Bastardkb/Dilemma/pics/1e.jpg

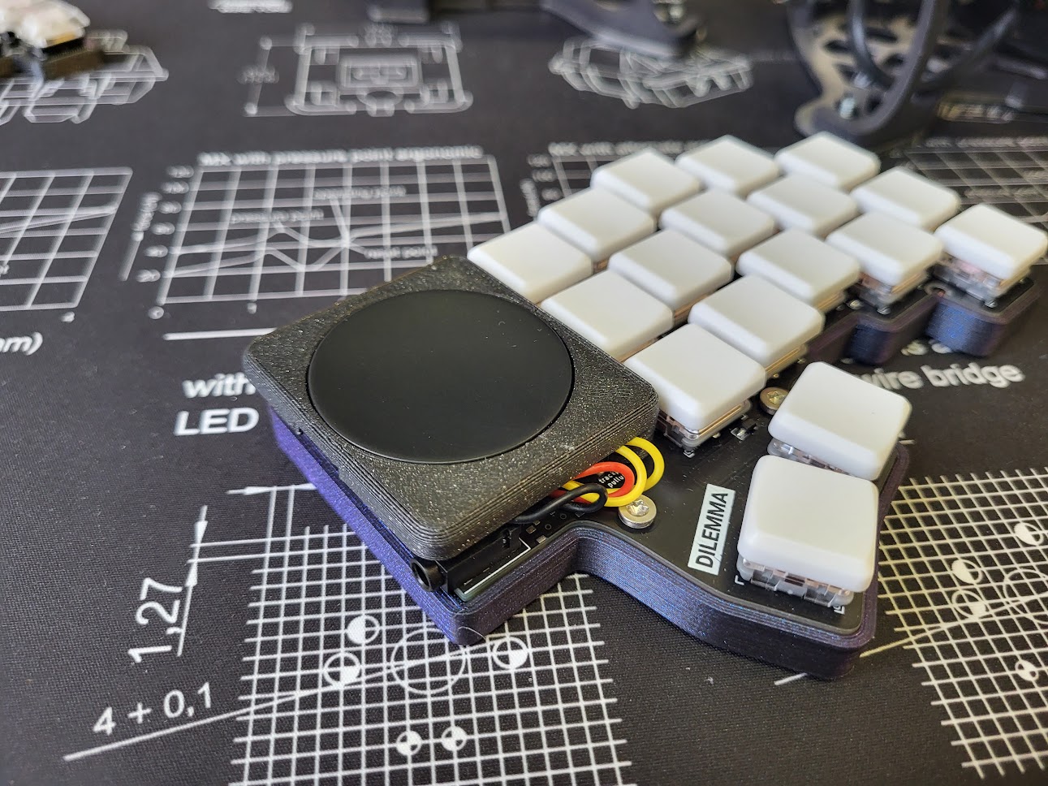
pics/1e.jpg
