Bastardkb/Dilemma/pics/1f.jpg

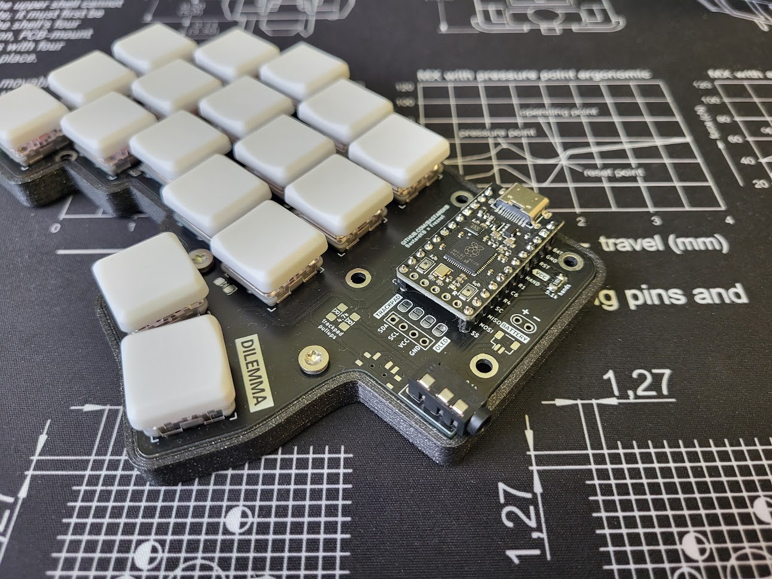
pics/1f.jpg
