Bastardkb/Dilemma/pics/1g.jpg

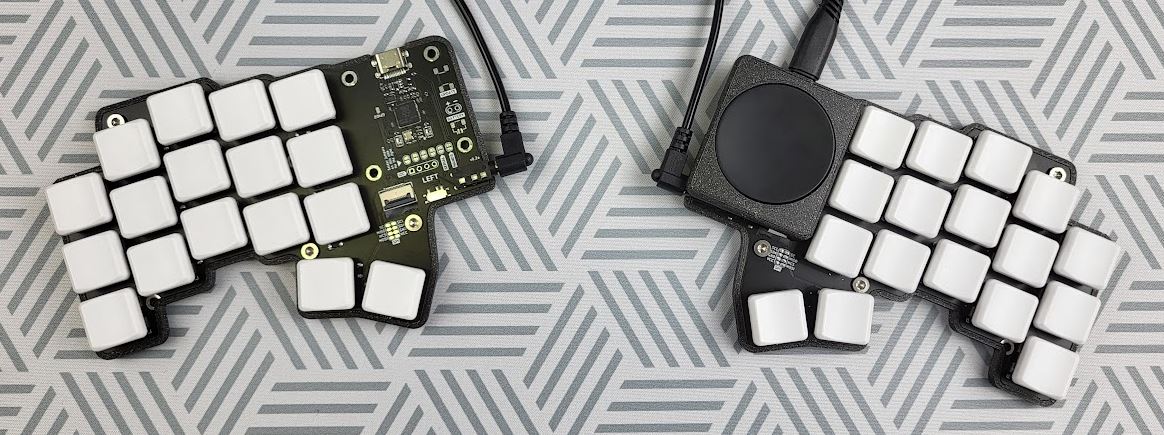
pics/1g.jpg
