Bastardkb/Dilemma/pics/1j.jpg

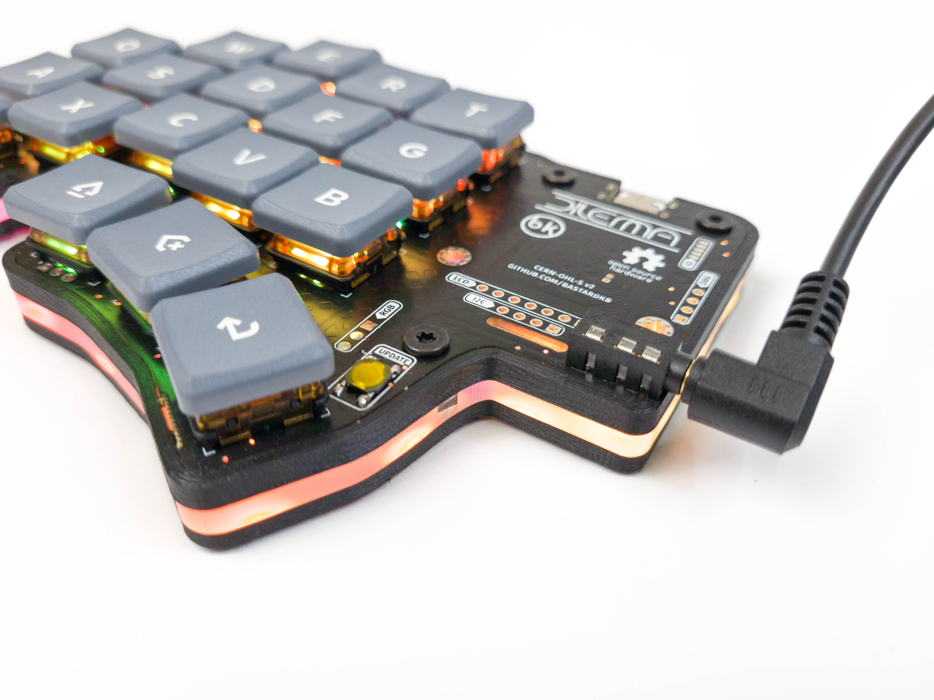
pics/1j.jpg
