Bastardkb/Dilemma/pics/1k.jpg

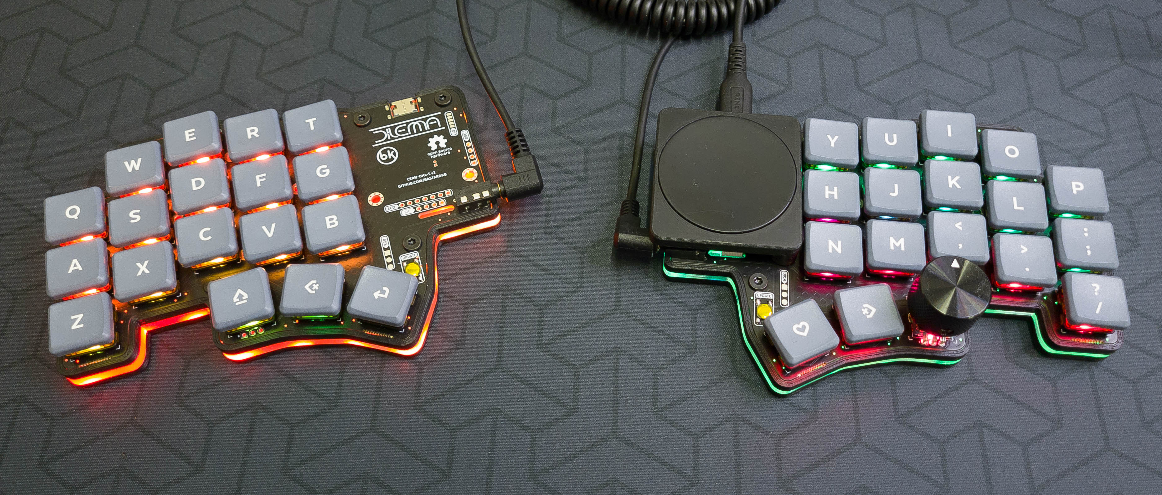
pics/1k.jpg
