Bastardkb/Dilemma/pics/1l.jpg

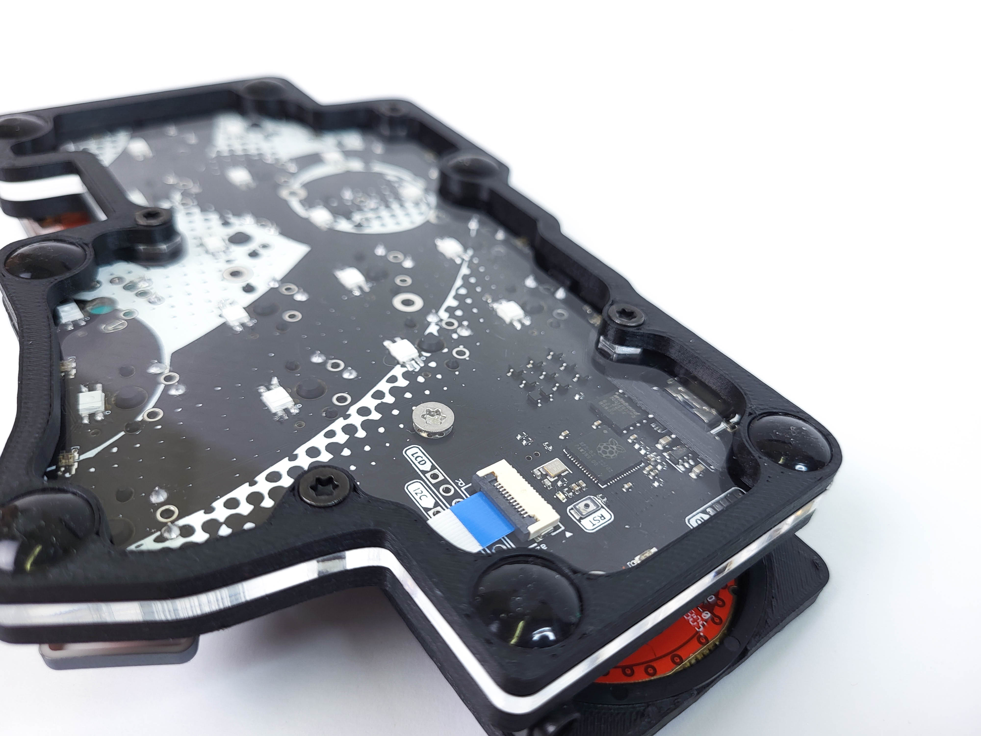
pics/1l.jpg
