Bastardkb/Dilemma/mechanical/trackpad/35mm/bottom2.stl

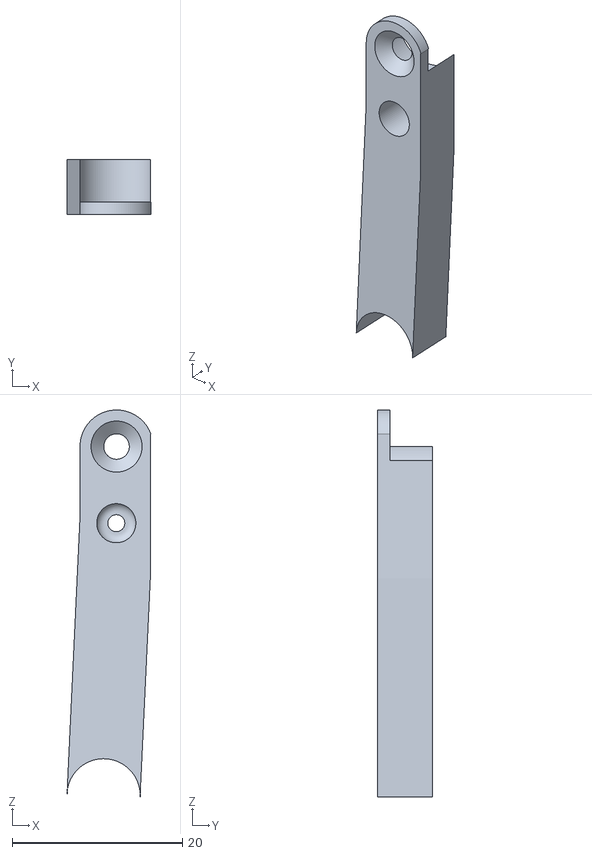
[picture p32: CAD file, 2022-06-21]
mechanical/trackpad/35mm/bottom2.stl
9.87 x 6.50 x 45.5
