Bastardkb/Dilemma/mechanical/trackpad/40mm/top.stl

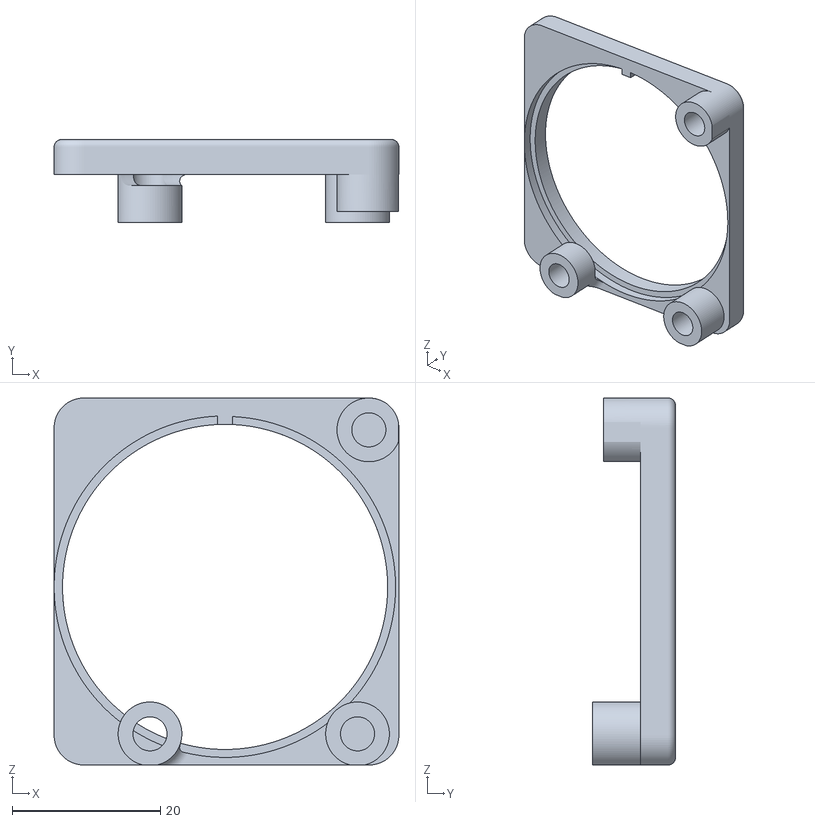
[picture p33: CAD file, 2022-10-11]
mechanical/trackpad/40mm/top.stl
46.5 x 11.2 x 49.5
