Bastardkb/Dilemma/mechanical/trackpad/procyon/hider_4x6.stl

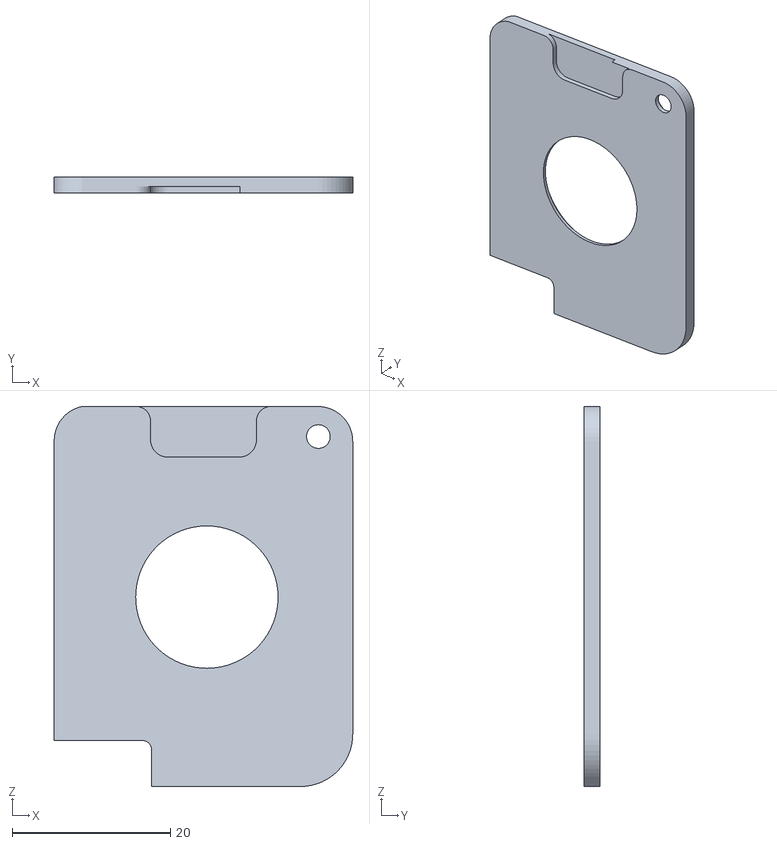
[picture p34: CAD file, 2025-09-29]
mechanical/trackpad/procyon/hider_4x6.stl
37.7 x 2.00 x 48.0
