Bastardkb/Dilemma/mods/3x5_3_mounts/dilemma_clamp_mount.stl

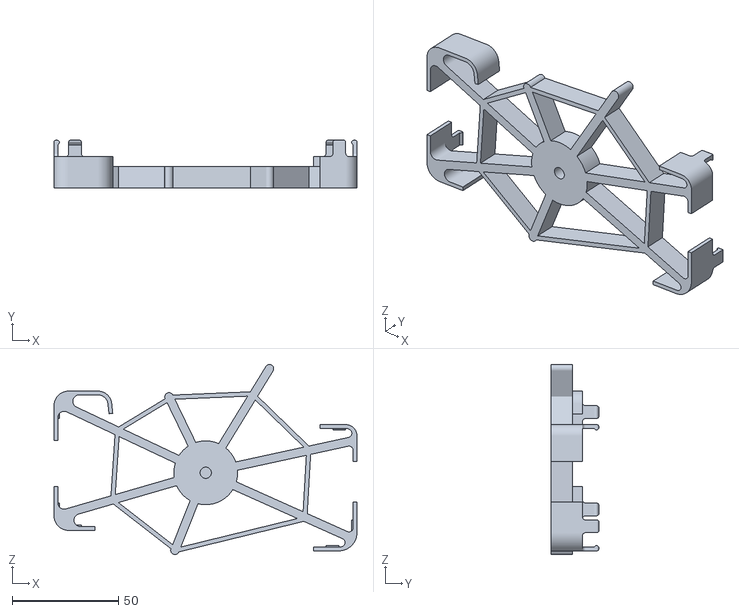
[picture p35: CAD file, 2025-11-19]
mods/3x5_3_mounts/dilemma_clamp_mount.stl
142.6 x 22.5 x 89.5
