Bastardkb/Dilemma/mods/40mm_flat_overlay/Short Alignment Key.stl

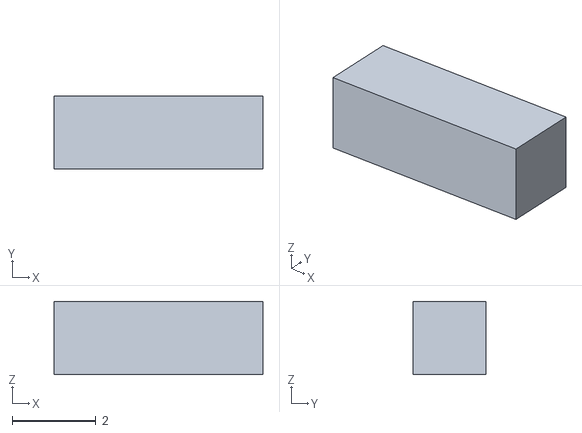
[picture p36: CAD file, 2022-11-09]
mods/40mm_flat_overlay/Short Alignment Key.stl
5.00 x 1.75 x 1.75
