Bastardkb/Dilemma/mods/4x6_4 tents/tent-5.stl

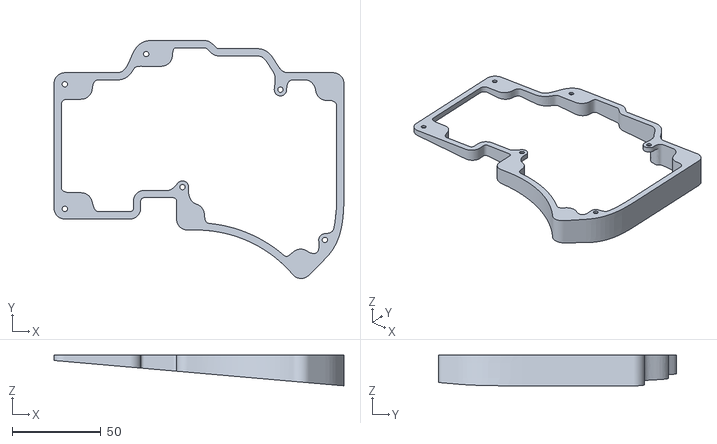
[picture p38: CAD file, 2025-08-07]
mods/4x6_4 tents/tent-5.stl
162.9 x 133.7 x 17.3
