Bastardkb/Dilemma/mods/cover/STEP/Blank Cover.STEP

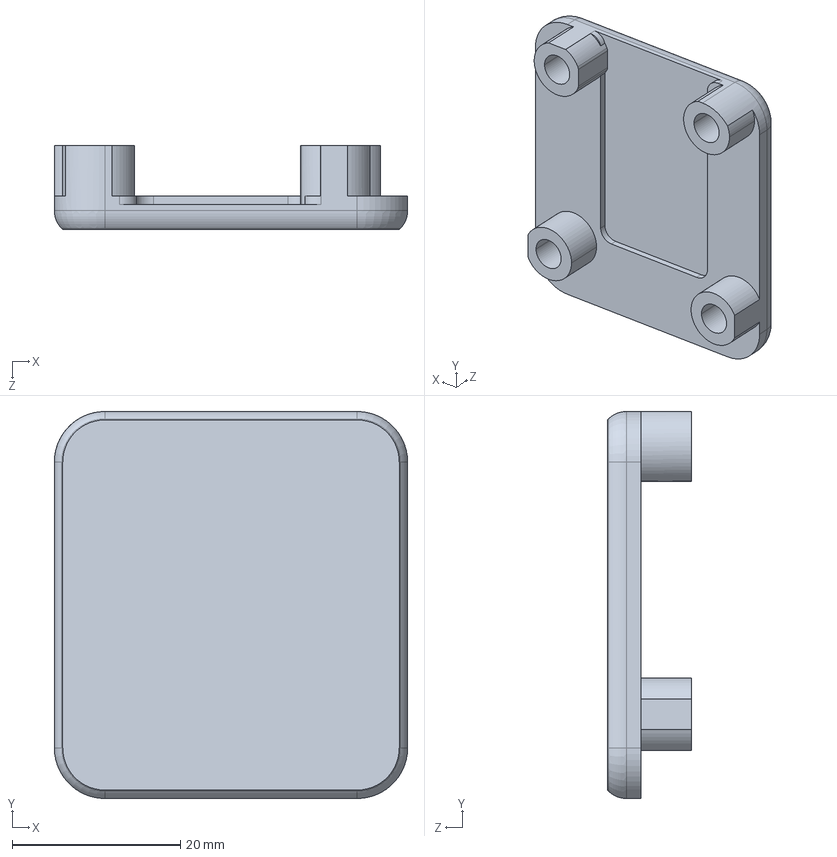
[picture p39: CAD file, 2022-11-09]
mods/cover/STEP/Blank Cover.STEP
42.0 x 46.0 x 10.0 mm
