Bastardkb/Dilemma/mods/trackball/trackball mount dilemma.stl

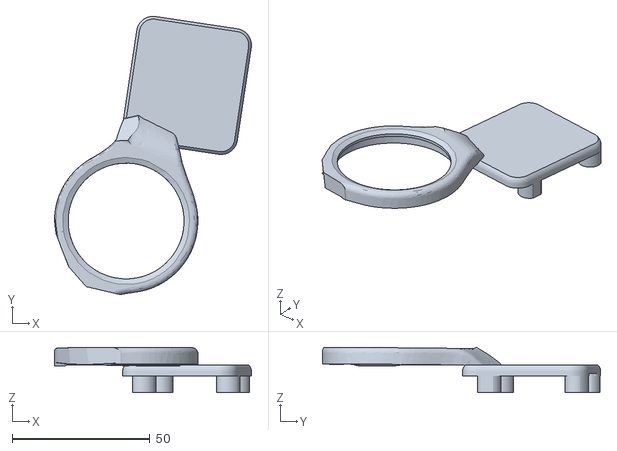
[picture p40: CAD file, 2026-09-03]
mods/trackball/trackball mount dilemma.stl
71.4 x 100.9 x 16.5
