Bastardkb/Dilemma/4x6_4/dilemma-Edge_Cuts.dxf

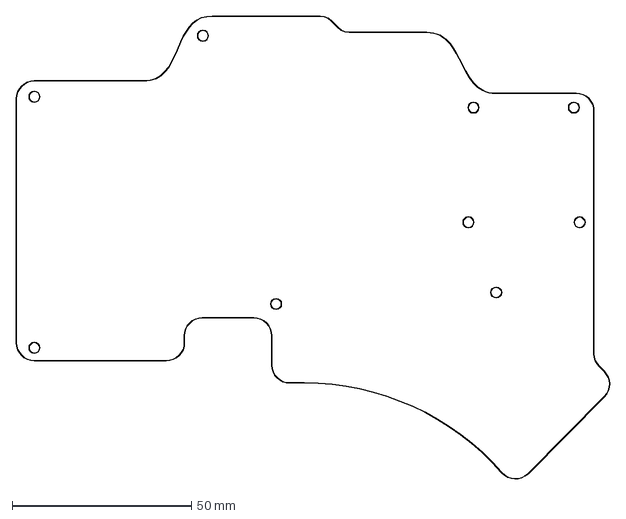
[picture p41: CAD file, 2023-09-18]
4x6_4/dilemma-Edge_Cuts.dxf
165.4 x 129.1 mm
