Bastardkb/Dilemma/mechanical/cases/3x5_2/tenting_puck_hex/STEP/Dilemma Case Tenting Puck Opening.STEP

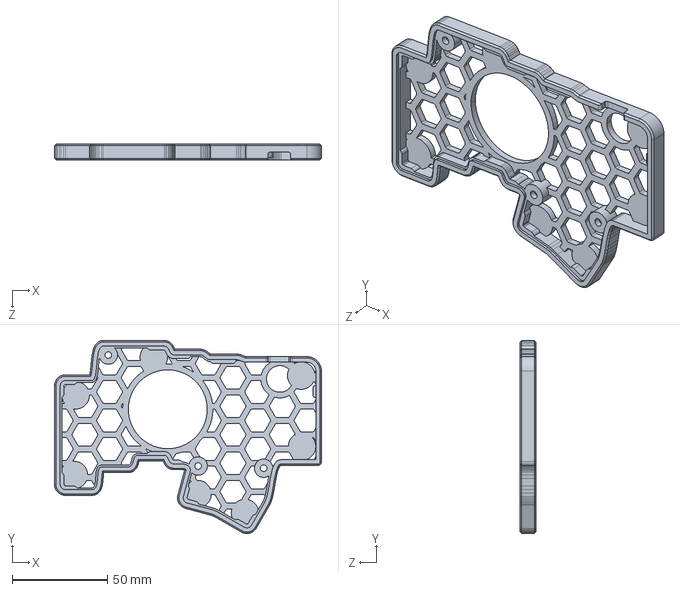
[picture p42: CAD file, 2022-11-09]
mechanical/cases/3x5_2/tenting_puck_hex/STEP/Dilemma Case Tenting Puck Opening.STEP
140.5 x 101.6 x 8.20 mm
