Bastardkb/Dilemma/mechanical/cases/3x5_3/bottom_metal.dxf

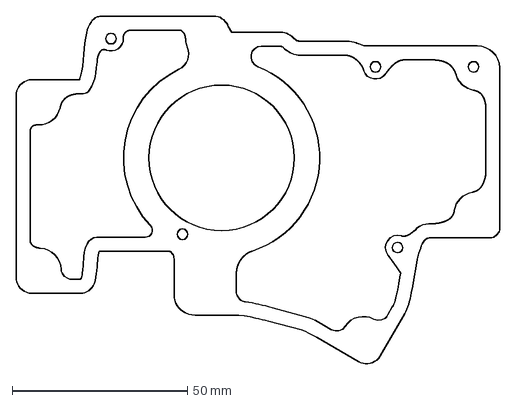
[picture p43: CAD file, 2023-03-31]
mechanical/cases/3x5_3/bottom_metal.dxf
138.0 x 99.2 mm
