Bastardkb/Dilemma/mechanical/cases/3x5_3_trackball/top right.stl

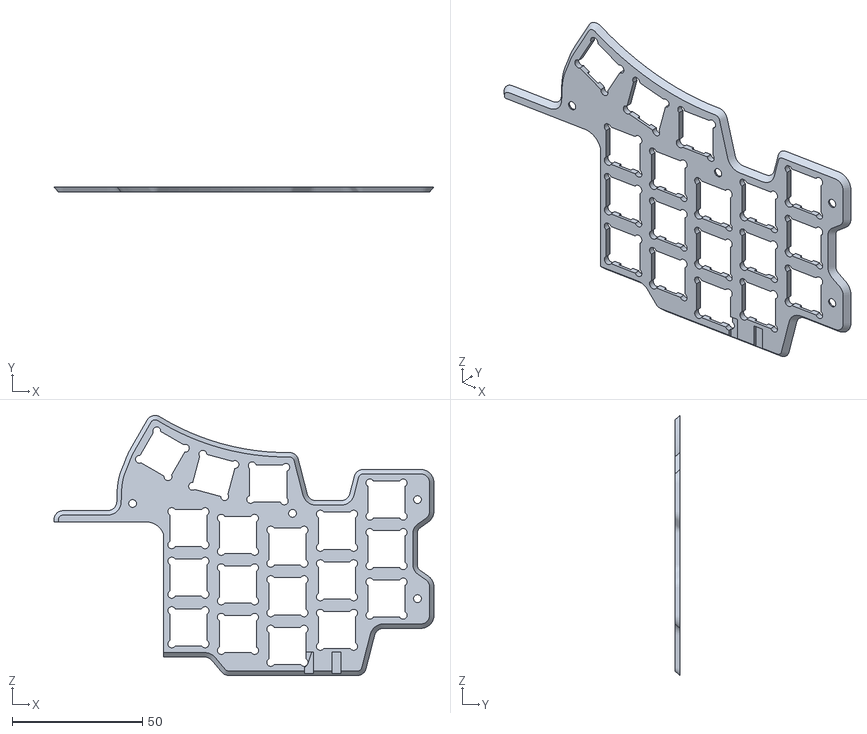
[picture p44: CAD file, 2026-09-10]
mechanical/cases/3x5_3_trackball/top right.stl
145.8 x 2.00 x 99.8
