Bastardkb/Dilemma/mechanical/cases/4x6_4/acrylic.stl

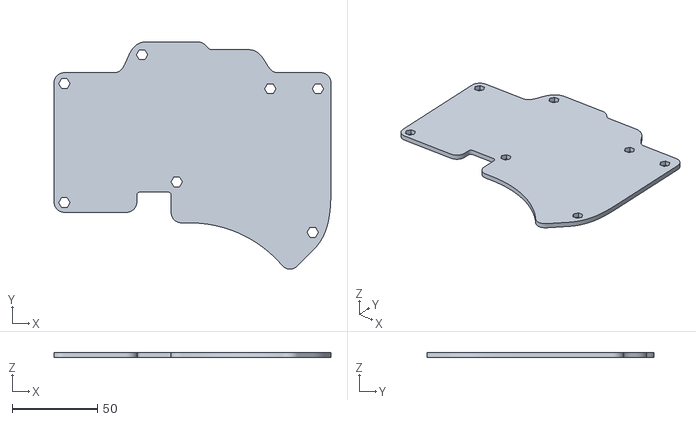
[picture p45: CAD file, 2024-01-12]
mechanical/cases/4x6_4/acrylic.stl
162.9 x 133.7 x 3.00
