Bastardkb/Dilemma/mechanical/cases/4x6_4/unibody/outer.stl

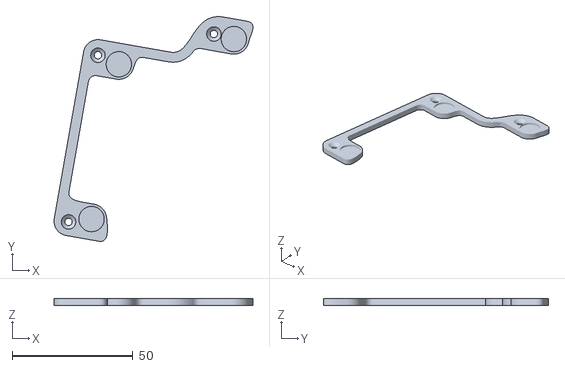
[picture p46: CAD file, 2023-10-04]
mechanical/cases/4x6_4/unibody/outer.stl
82.3 x 93.0 x 3.00
