Bastardkb/Dilemma/mechanical/trackball/trackball holder top.stl

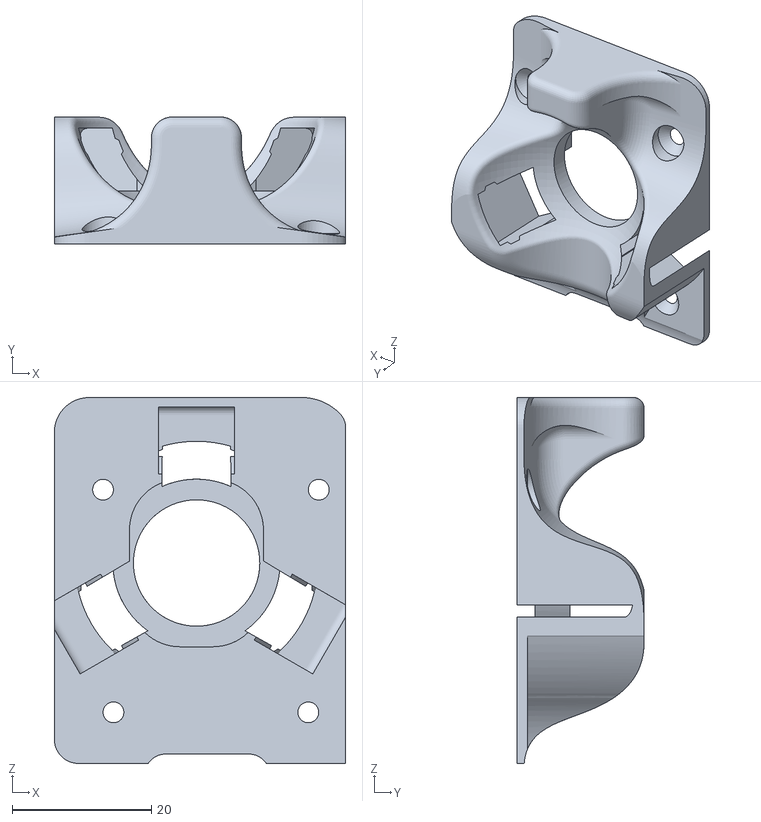
[picture p47: CAD file, 2026-09-01]
mechanical/trackball/trackball holder top.stl
41.9 x 18.3 x 52.6
