Bastardkb/Dilemma/mechanical/trackpad/35mm/top.stl

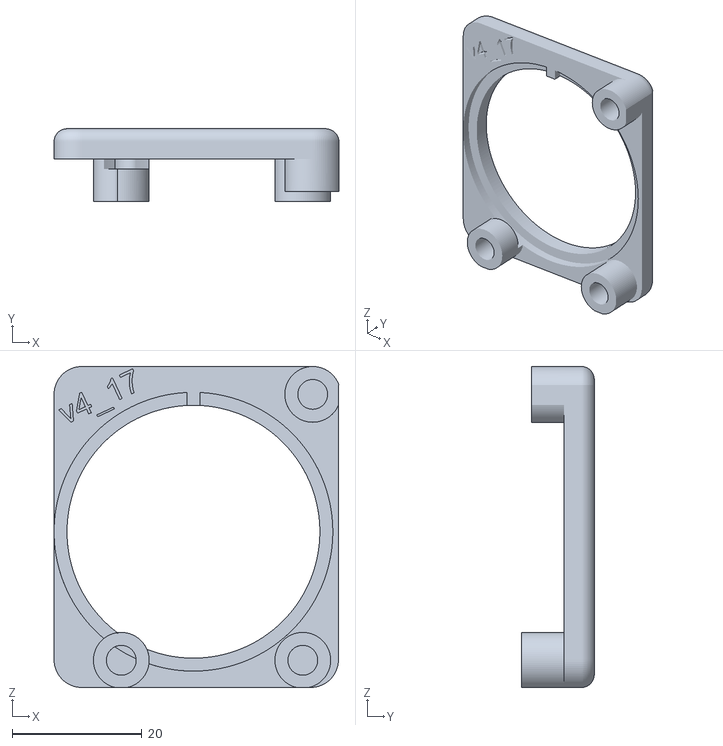
[picture p48: CAD file, 2022-06-21]
mechanical/trackpad/35mm/top.stl
43.9 x 11.2 x 49.5
