Bastardkb/Dilemma/mechanical/trackpad/procyon/spacer.stl

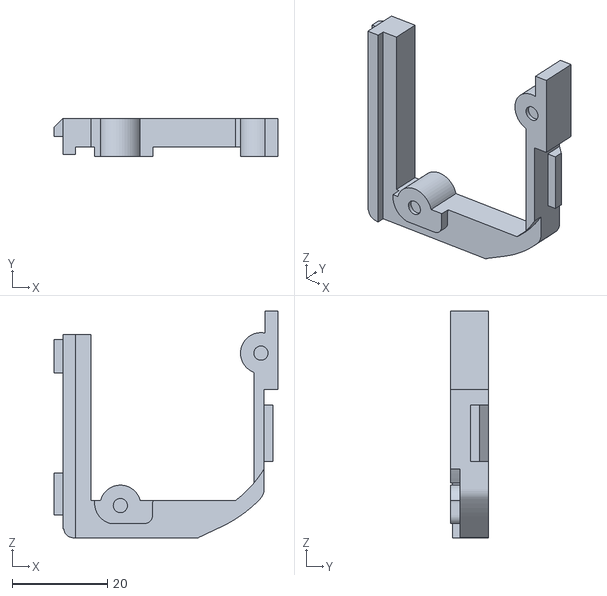
[picture p49: CAD file, 2025-08-08]
mechanical/trackpad/procyon/spacer.stl
47.0 x 8.00 x 47.6
