Bastardkb/Dilemma/mods/3x5_3_mounts/dilemma_table_tent.stl

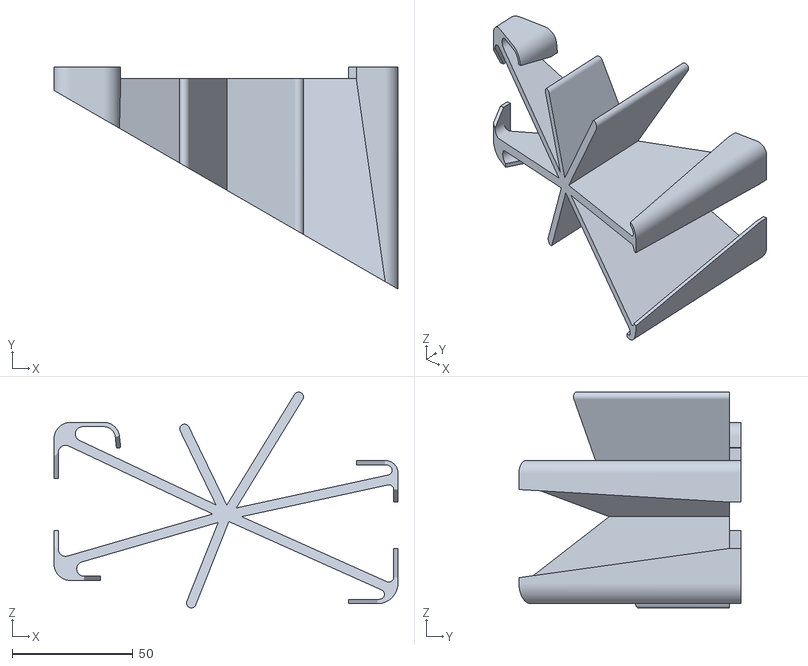
[picture p50: CAD file, 2025-11-19]
mods/3x5_3_mounts/dilemma_table_tent.stl
142.6 x 92.1 x 89.5
