Bastardkb/Dilemma/mods/40mm_flat_overlay/Long Alignment Key.stl

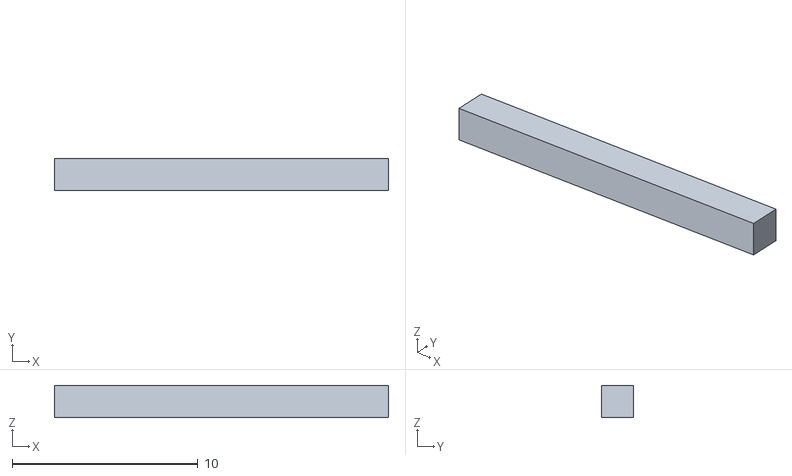
[picture p51: CAD file, 2022-11-09]
mods/40mm_flat_overlay/Long Alignment Key.stl
18.0 x 1.75 x 1.75
