Bastardkb/Dilemma/mods/40mm_flat_overlay/STEP/Cirque TM040040-2024-302 Holder Top.STEP

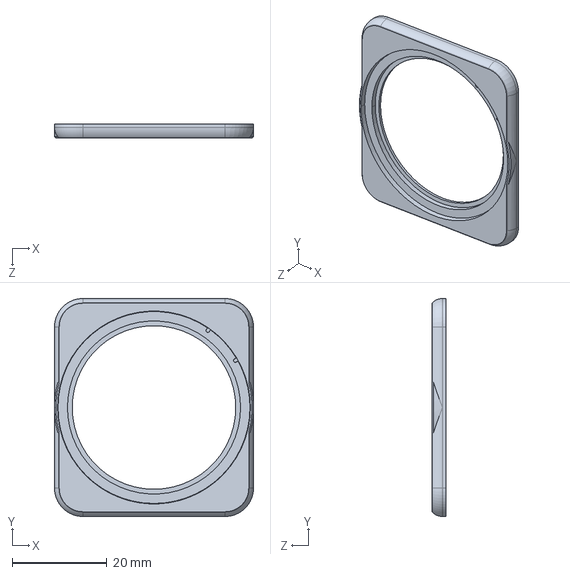
[picture p52: CAD file, 2022-11-09]
mods/40mm_flat_overlay/STEP/Cirque TM040040-2024-302 Holder Top.STEP
42.0 x 46.0 x 3.00 mm
