Bastardkb/Dilemma/mechanical/cases/3x5_3_hotswap/midplate.dxf

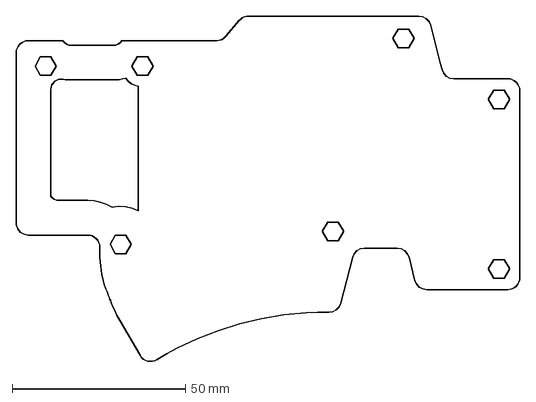
[picture p54: CAD file, 2025-04-01]
mechanical/cases/3x5_3_hotswap/midplate.dxf
145.5 x 99.9 mm
