Bastardkb/Dilemma/mechanical/cases/3x5_3_trackball/spacer.stl

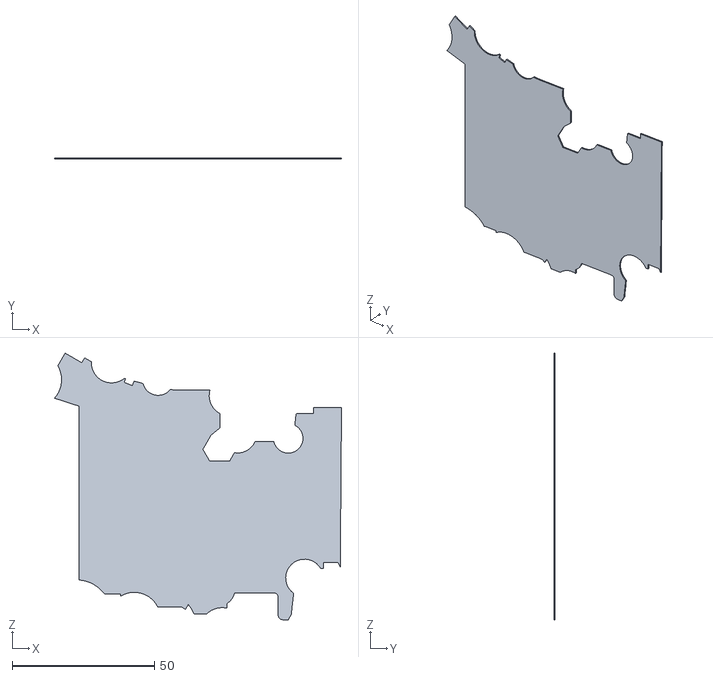
[picture p55: CAD file, 2026-09-10]
mechanical/cases/3x5_3_trackball/spacer.stl
101.0 x 0.5 x 93.8
