Bastardkb/Dilemma/mechanical/cases/4x6_4/bottom.3mf

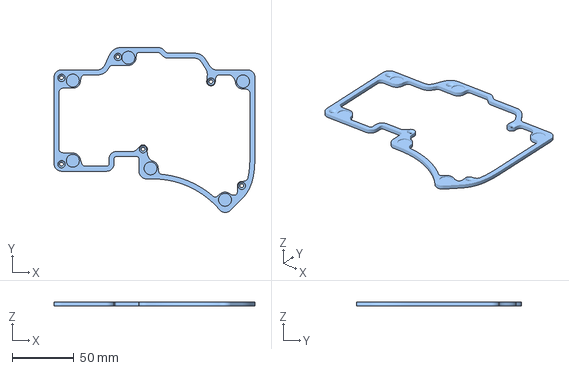
[picture p56: CAD file, 2023-09-18]
mechanical/cases/4x6_4/bottom.3mf
162.9 x 133.7 x 3.00 mm
