Bastardkb/Dilemma/mechanical/cases/4x6_4_hotswap/mid.stl

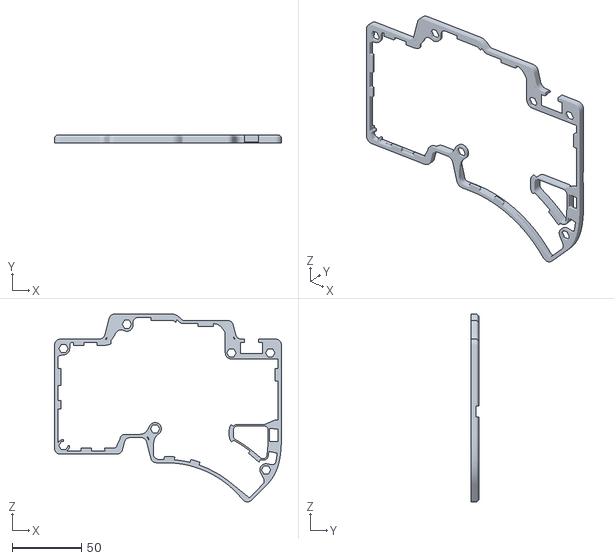
[picture p57: CAD file, 2025-09-29]
mechanical/cases/4x6_4_hotswap/mid.stl
163.7 x 5.47 x 135.6
