Bastardkb/Dilemma/mechanical/trackpad/35mm/bottom1.stl

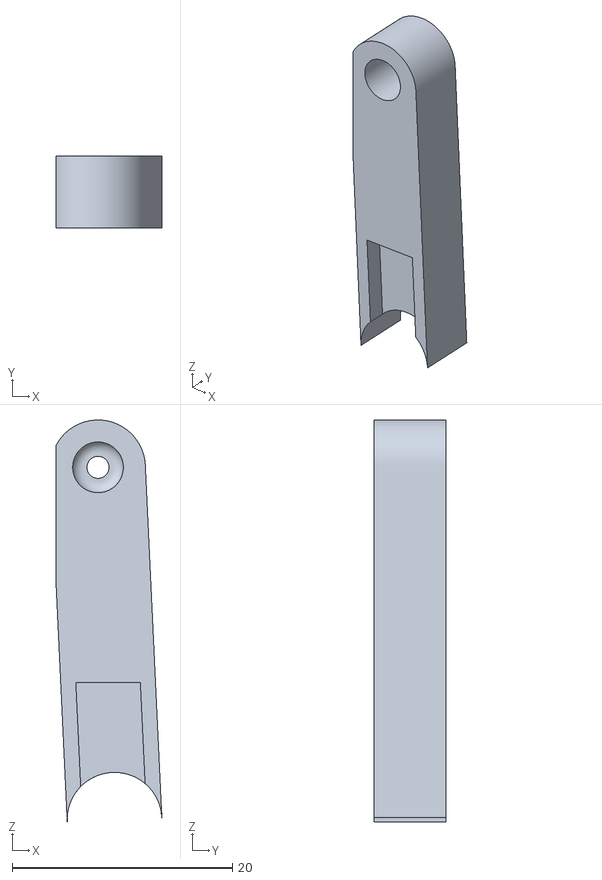
[picture p58: CAD file, 2022-06-21]
mechanical/trackpad/35mm/bottom1.stl
9.60 x 6.50 x 36.5
