Bastardkb/Dilemma/mechanical/trackpad/40mm/bottom1.stl

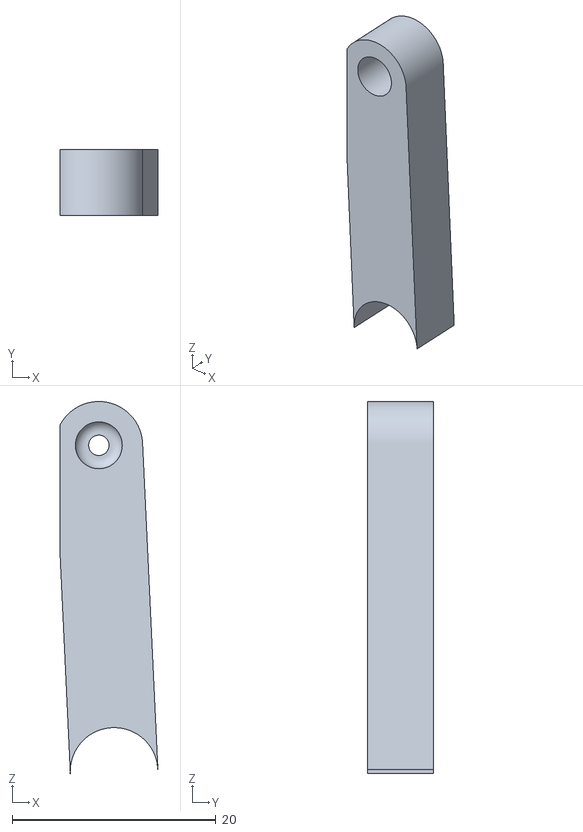
[picture p59: CAD file, 2022-10-11]
mechanical/trackpad/40mm/bottom1.stl
9.60 x 6.50 x 36.5
