Bastardkb/Dilemma/mechanical/trackpad/procyon/holder.stl

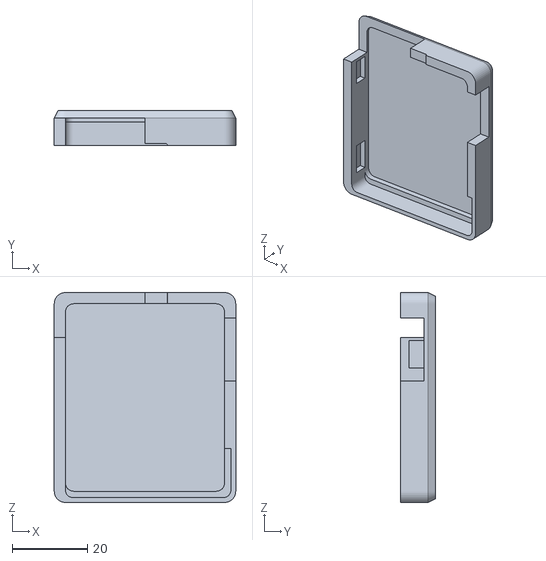
[picture p60: CAD file, 2025-08-08]
mechanical/trackpad/procyon/holder.stl
48.4 x 9.20 x 56.0
