Bastardkb/Dilemma/mods/4x6_4 tents/tent-7.stl

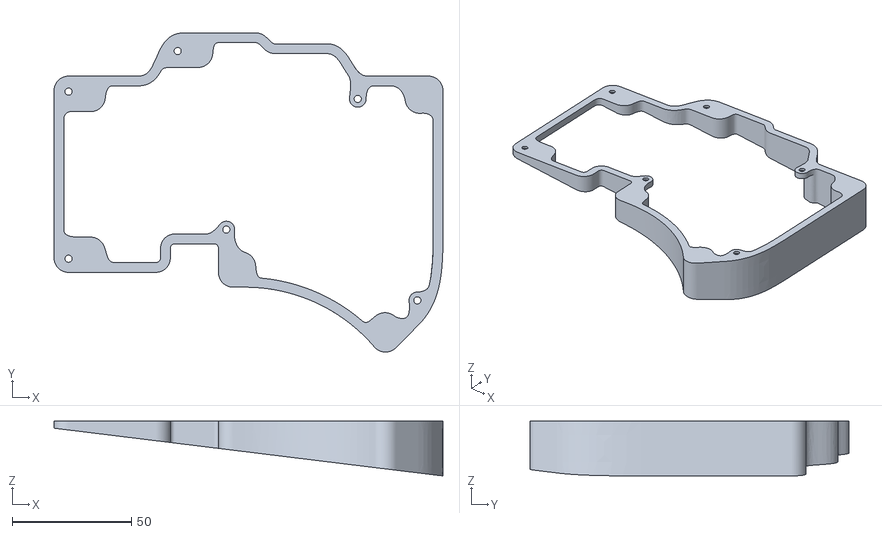
[picture p61: CAD file, 2025-08-07]
mods/4x6_4 tents/tent-7.stl
162.9 x 133.7 x 23.0
