Bastardkb/Dilemma/mechanical/cases/3x5_3_trackball/contour.stl

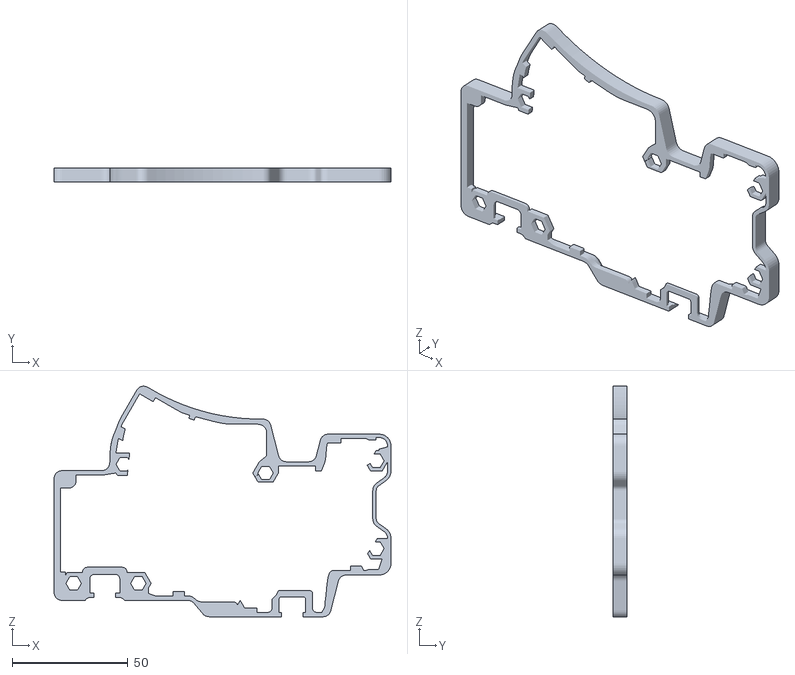
[picture p62: CAD file, 2026-09-01]
mechanical/cases/3x5_3_trackball/contour.stl
145.8 x 6.07 x 99.8
