Bastardkb/Dilemma/mechanical/cases/4x6_4_hotswap/bottom.stl

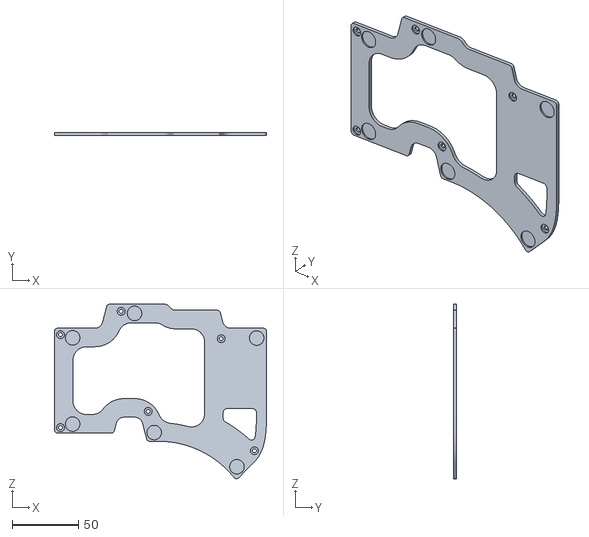
[picture p63: CAD file, 2025-09-29]
mechanical/cases/4x6_4_hotswap/bottom.stl
159.7 x 2.23 x 131.6
