Bastardkb/Dilemma/mechanical/trackpad/procyon/hider_3x5.stl

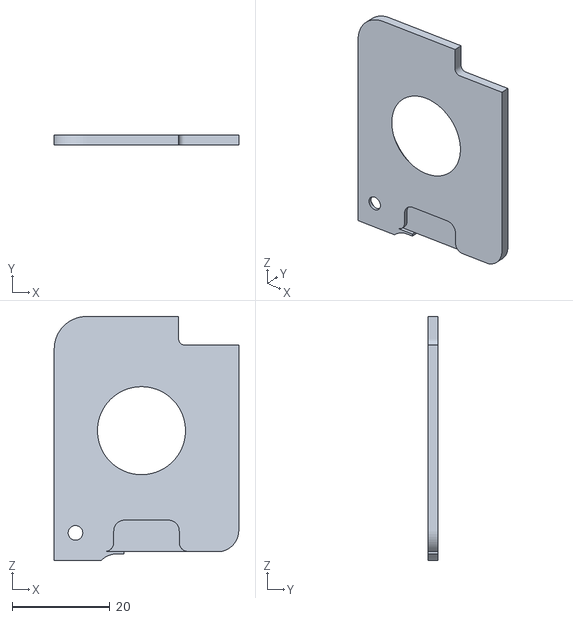
[picture p64: CAD file, 2025-05-29]
mechanical/trackpad/procyon/hider_3x5.stl
37.7 x 2.00 x 49.9
