Bastardkb/Dilemma/mechanical/cases/3x5_3/bottom.stl

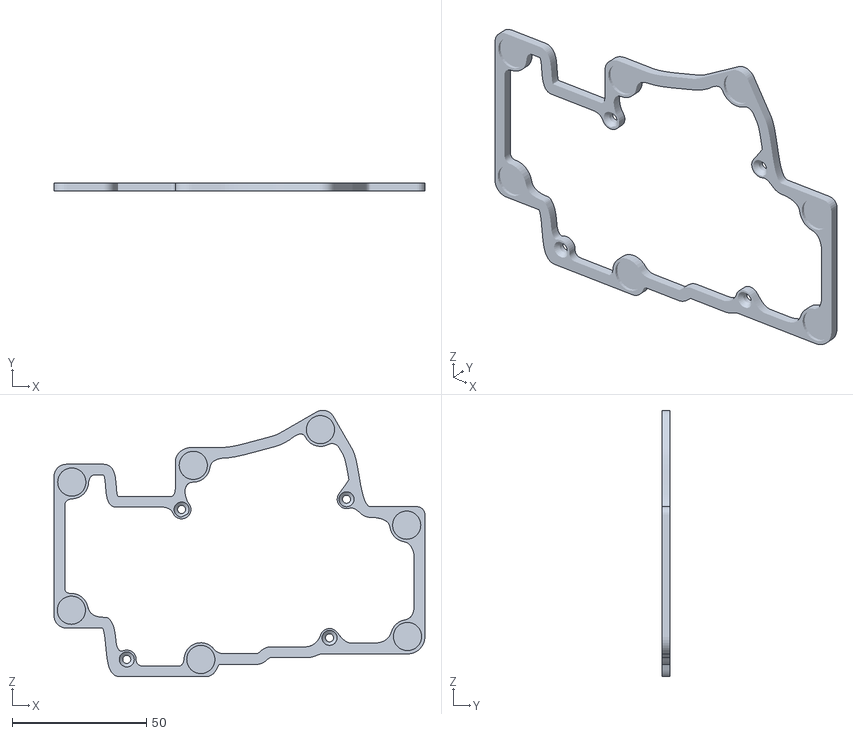
[picture p65: CAD file, 2023-03-31]
mechanical/cases/3x5_3/bottom.stl
138.0 x 3.00 x 99.1
