Bastardkb/Dilemma/mechanical/cases/3x5_3_trackball/bottom.stl

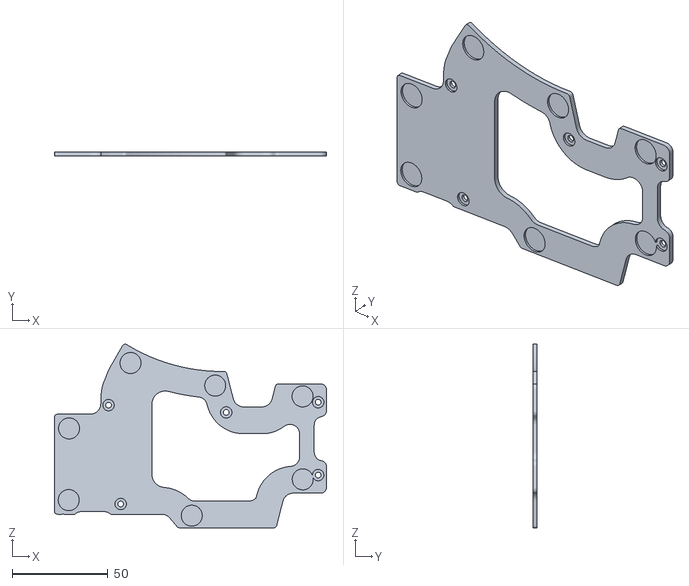
[picture p66: CAD file, 2026-09-01]
mechanical/cases/3x5_3_trackball/bottom.stl
141.8 x 2.23 x 95.8
